Obrelix/Arduino-Uno-Rover-with-PS4-Controller/Images/IMG_20231026_203336.jpg

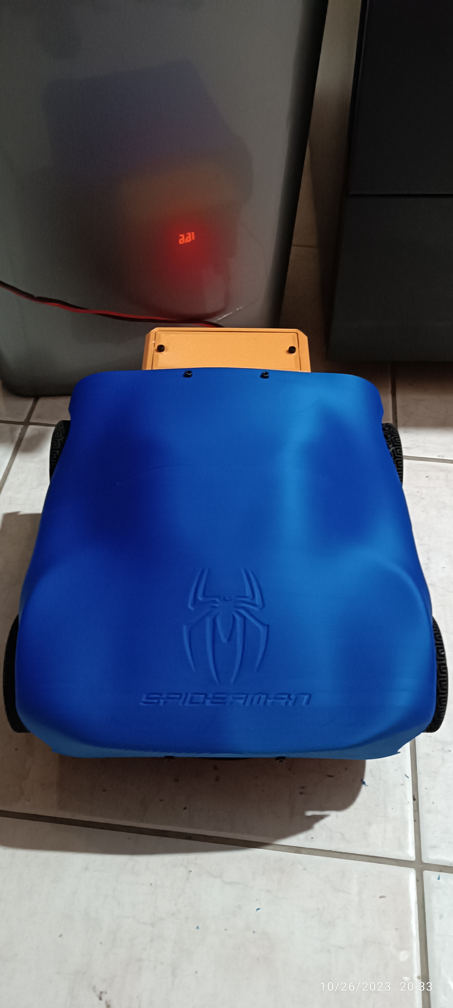
Images/IMG_20231026_203336.jpg
