Obrelix/Arduino-Uno-Rover-with-PS4-Controller/Images/IMG_20231029_165855.jpg

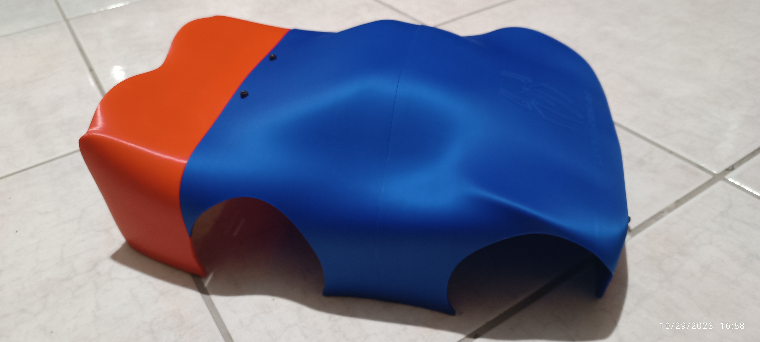
Images/IMG_20231029_165855.jpg
